phorton1/Arduino-teensyExpression/docs/ftp/hardware_patches.csv

Patch No: | Patch Name: | Patch Hold Mode: | Patch Split Low: | Patch Split High: | Patch Arp. Mode: | Patch Arp. Speed: | Patch Arp. Length: | Patch Pick Sens.: | Sound1 Program: | Sound1 Bank LSB: | Sound1 Bank MSB: | Sound1 Quantize Mode: | Sound1 Transpose: | Sound1 Volume: | Sound1 Dynamics Sens: | Sound1 Dynamics Offs: | Sound1 Reverb: | Sound2 Program: | Sound2 Bank LSB: | Sound2 Bank MSB: | Sound2 Quantize Mode: | Sound2 Transpose: | Sound2 Volume: | Sound2 Dynamics Sens: | Sound2 Dynamics Offs: | Sound2 Reverb: | Sound3 Program: | Sound3 Bank LSB: | Sound3 Bank MSB: | Sound3 Quantize Mode: | Sound3 Transpose: | Sound3 Volume: | Sound3 Dynamics Sens: | Sound3 Dynamics Offs: | Sound3 Reverb: | Sound4 Program: | Sound4 Bank LSB: | Sound4 Bank MSB: | Sound4 Quantize Mode: | Sound4 Transpose: | Sound4 Volume: | Sound4 Dynamics Sens: | Sound4 Dynamics Offs: | Sound4 Reverb: | Hold Program: | Hold Bank LSB: | Hold Bank MSB: | Hold Quantize Mode: | Hold Transpose: | Hold Volume: | Hold Dynamics Sens: | Hold Dynamics Offs: | Hold Reverb: | Mono/Poly: | Sound1 Enable: | Sound2 Enable: | Sound3 Enable: | Sound4 Enable: | Hold Enable:
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
