phorton1/Arduino-teensyExpression/docs/images/hardware-board_v7.big.jpg

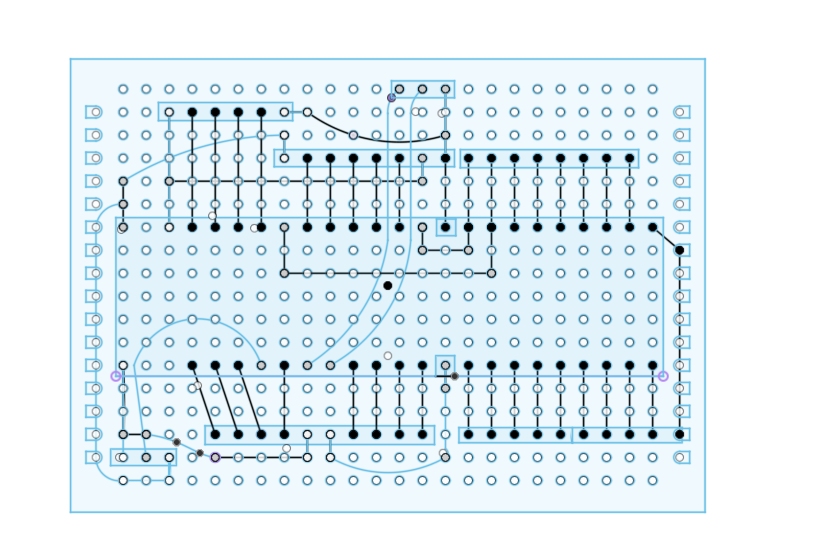
docs/images/hardware-board_v7.big.jpg
