phorton1/Arduino-teensyExpression/docs/images/hardware-micro_usb.jpg

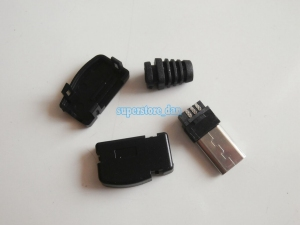
docs/images/hardware-micro_usb.jpg
