phorton1/Arduino-teensyExpression/docs/images/hardware-serial_port.big.jpg

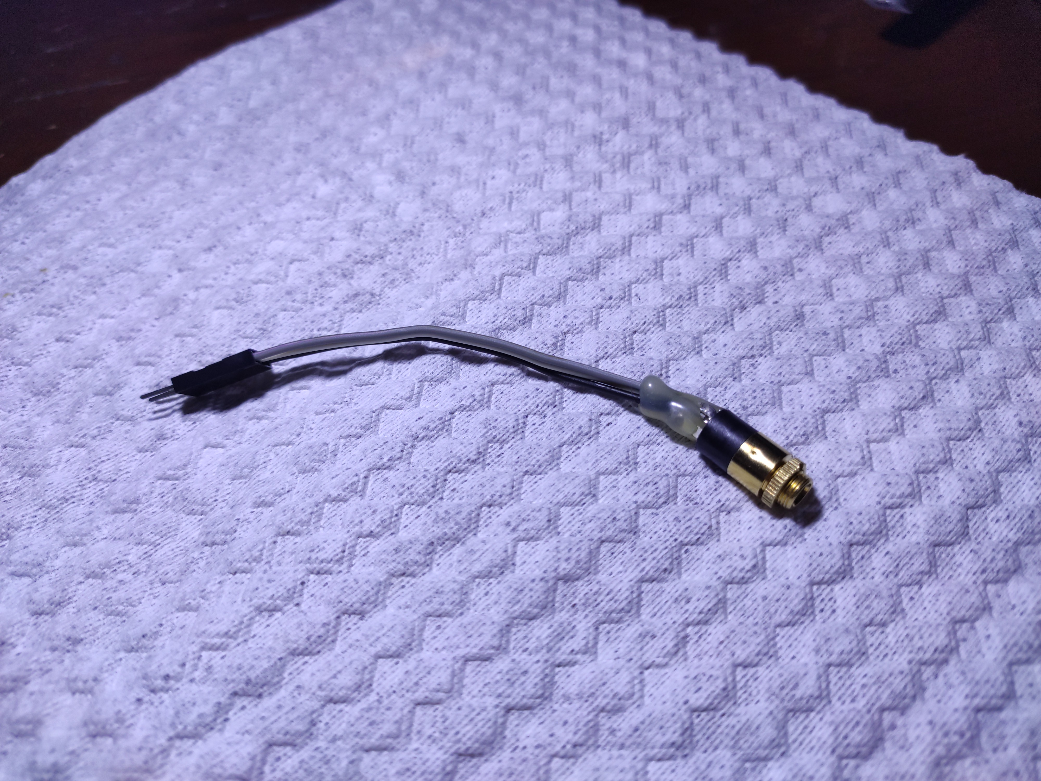
docs/images/hardware-serial_port.big.jpg
