phorton1/Arduino-teensyExpression/docs/images/teensyExpression17.jpg

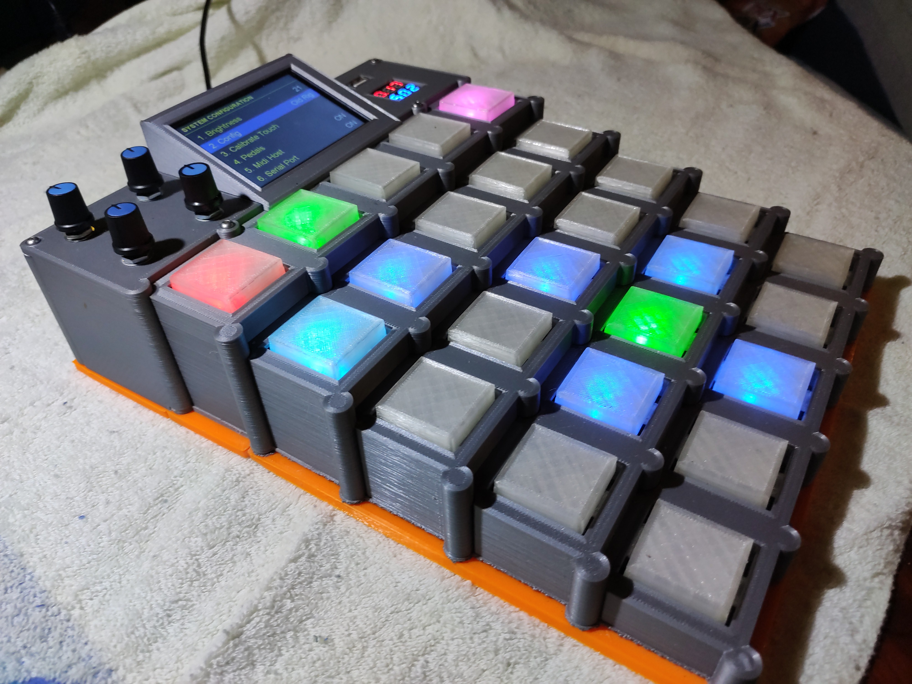
docs/images/teensyExpression17.jpg
