phorton1/Arduino-teensyExpression/docs/images/ui_configMidiMonitor.jpg

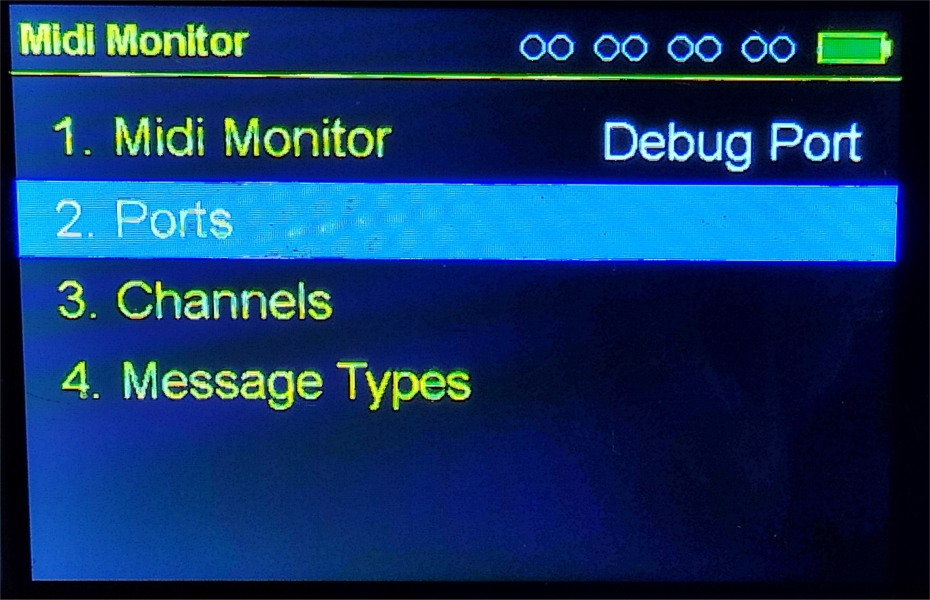
docs/images/ui_configMidiMonitor.jpg
