phorton1/Arduino-teensyExpression/docs/images/ui_configSystem_wide.jpg

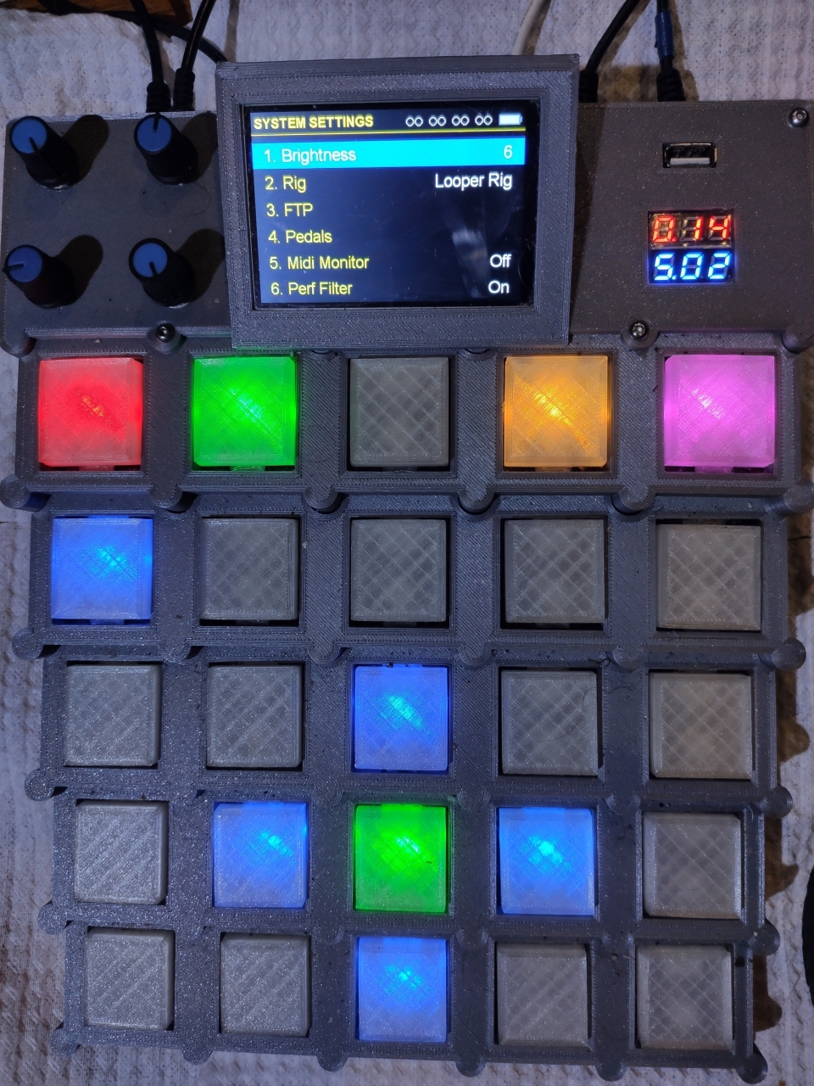
docs/images/ui_configSystem_wide.jpg
