phorton1/Arduino-teensyExpression/docs/images/ui_LooperRig_wide.jpg

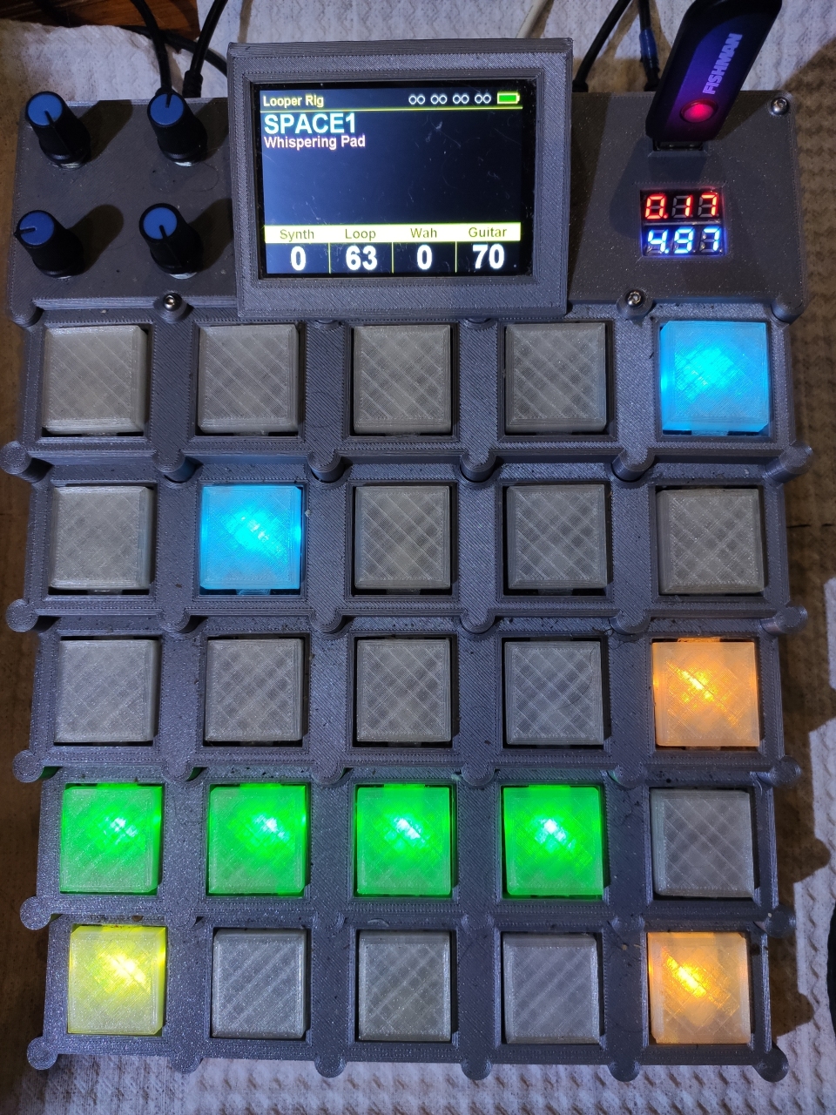
docs/images/ui_LooperRig_wide.jpg
