phorton1/Arduino-teensyExpression/docs/images/ui_LooperRig_withSong.jpg

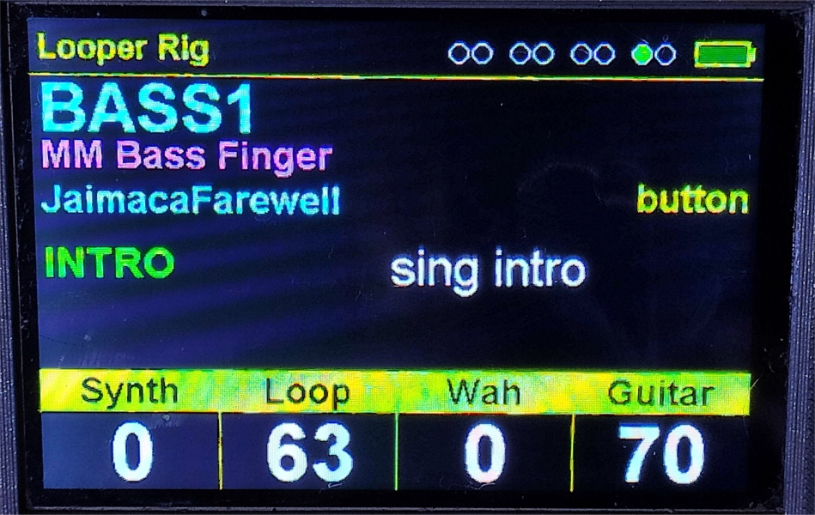
docs/images/ui_LooperRig_withSong.jpg
