phorton1/Arduino-teensyExpression/docs/images/ui_QuickMode_wide.jpg

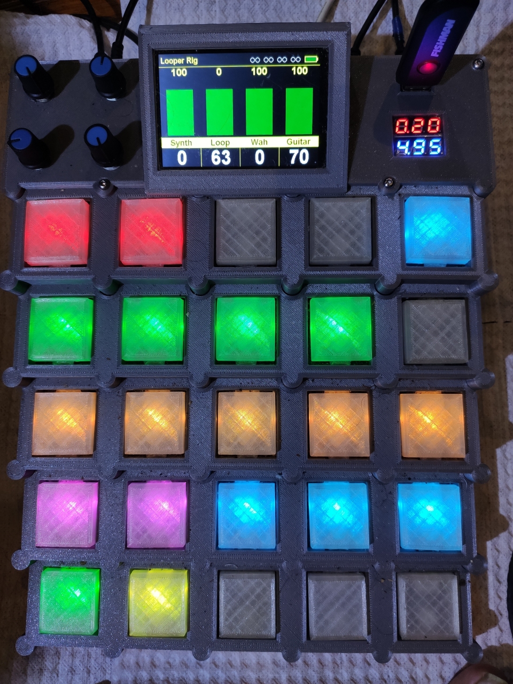
docs/images/ui_QuickMode_wide.jpg
