phorton1/Arduino-teensyExpression/docs/images/ui_selectSong.jpg

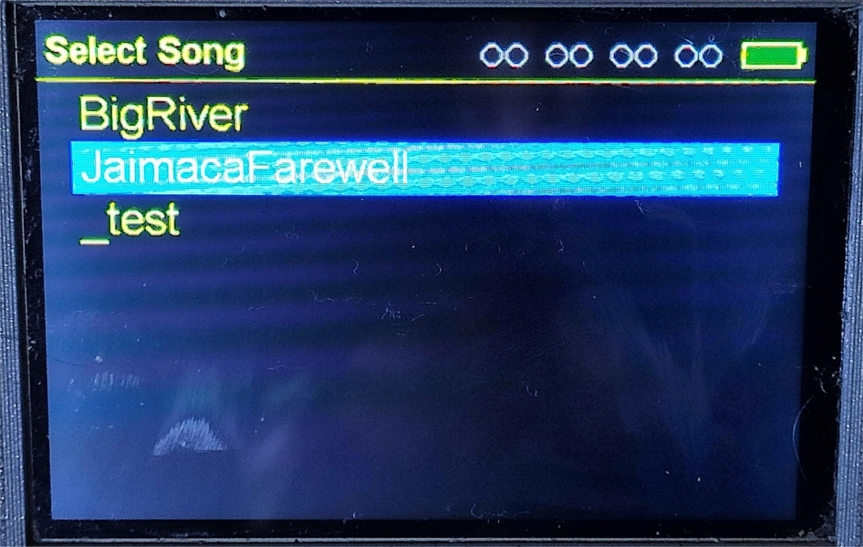
docs/images/ui_selectSong.jpg
