phorton1/Arduino-teensyExpression/docs/images/ui_songText.jpg

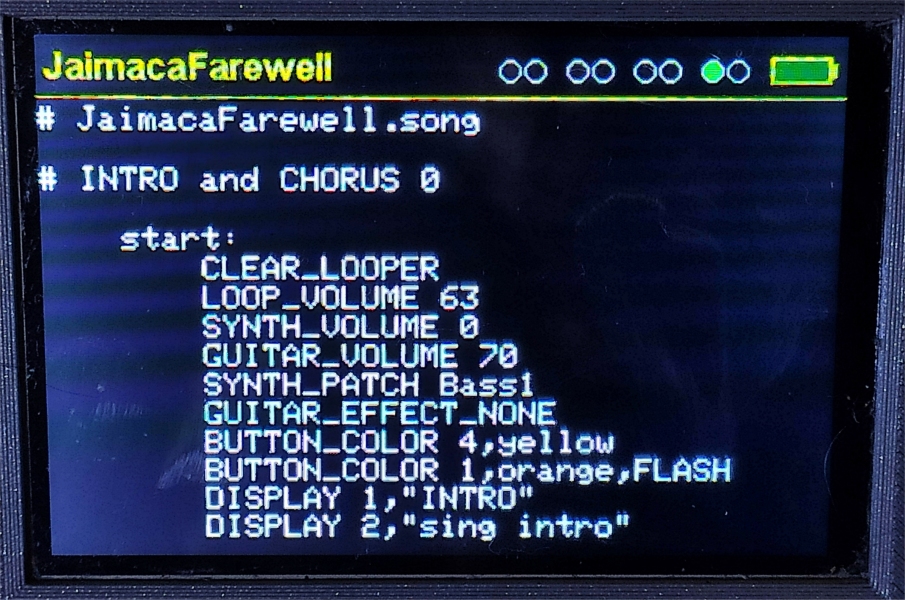
docs/images/ui_songText.jpg
