phorton1/Arduino-teensyExpression/docs/stl/display_case.stl

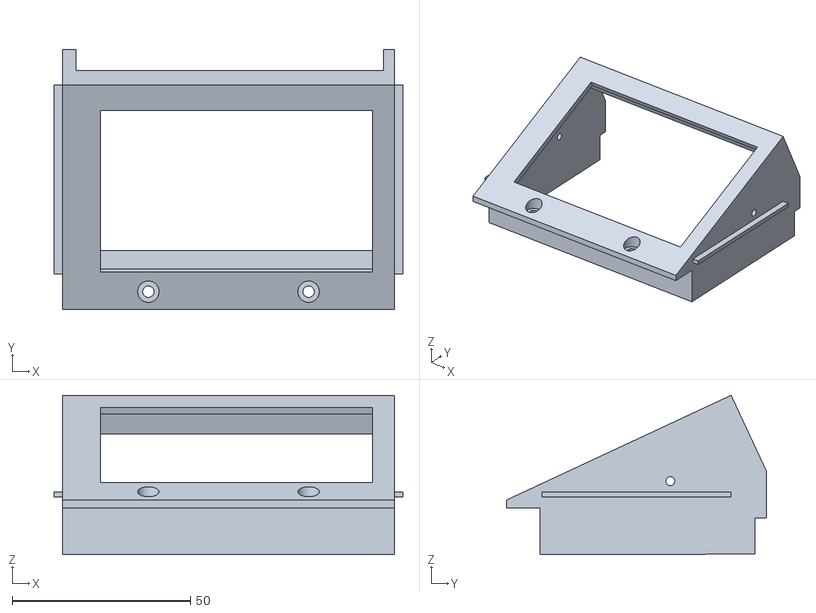
[picture p77: CAD file, 2025-01-11]
docs/stl/display_case.stl
98.0 x 73.0 x 44.8
