phorton1/Arduino-teensyExpression/docs/prusa/top5.3mf

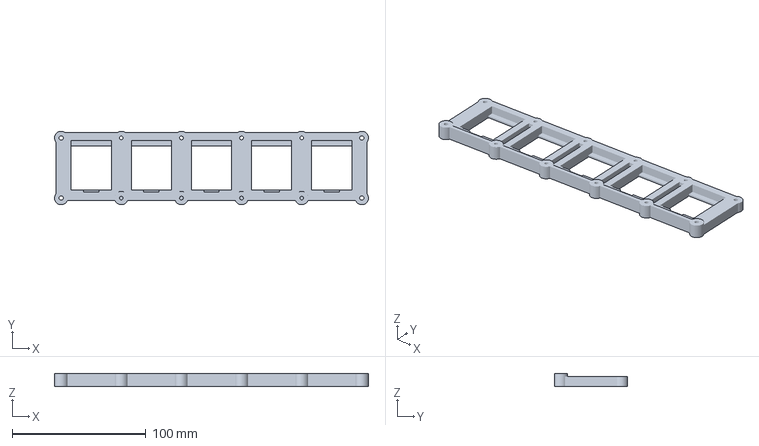
[picture p78: CAD file, 2025-01-11]
docs/prusa/top5.3mf
235.0 x 55.0 x 9.80 mm
