phorton1/Arduino-teensyExpression/docs/prusa/top_left.3mf

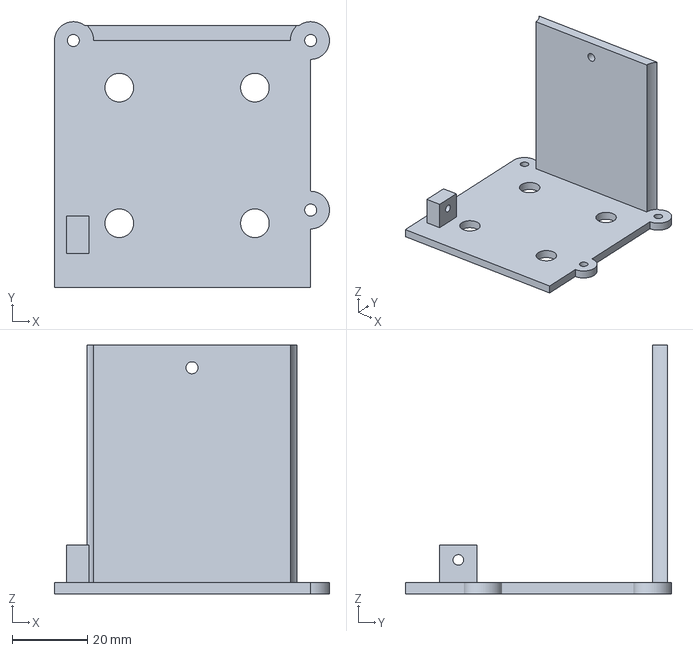
[picture p79: CAD file, 2025-01-11]
docs/prusa/top_left.3mf
73.0 x 70.5 x 66.0 mm
