phorton1/Arduino-teensyExpression/docs/stl/display_insert.stl

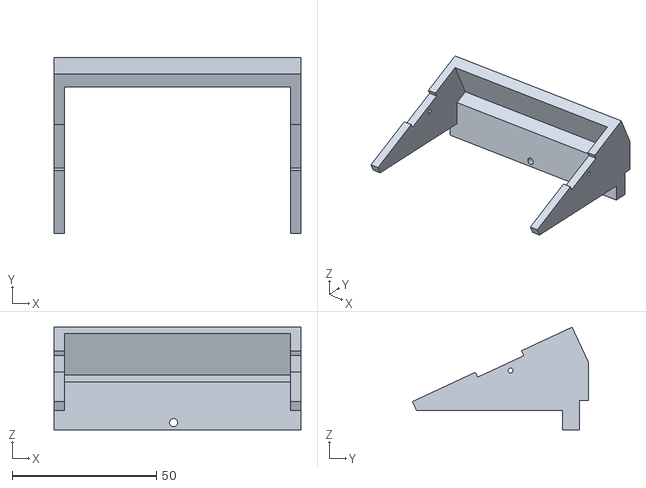
[picture p80: CAD file, 2025-01-11]
docs/stl/display_insert.stl
85.5 x 61.0 x 35.5
