phorton1/Arduino-teensyExpression/docs/prusa/display_insert.3mf

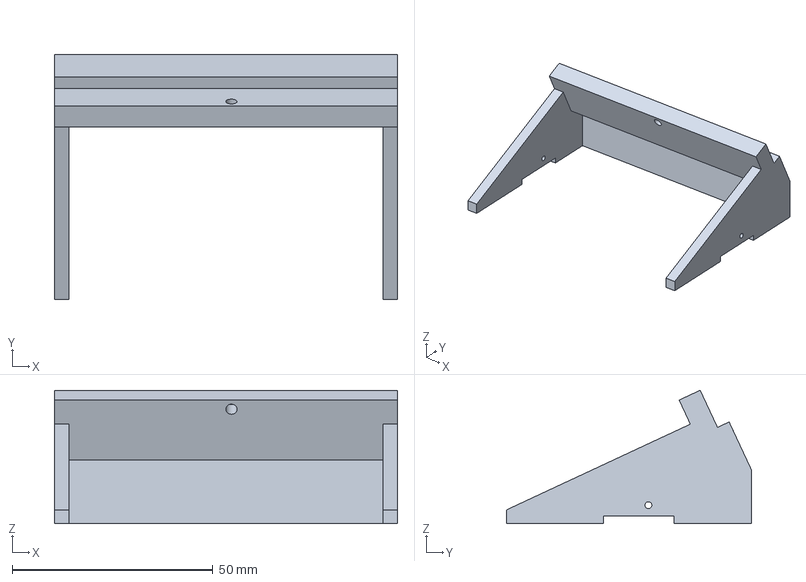
[picture p81: CAD file, 2025-01-11]
docs/prusa/display_insert.3mf
85.5 x 61.0 x 33.3 mm
