phorton1/Arduino-teensyExpression/docs/stl/frame3.stl

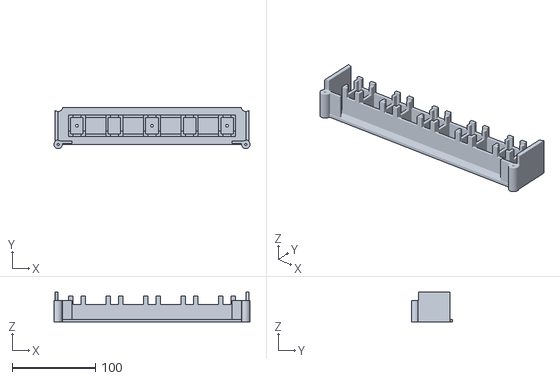
[picture p82: CAD file, 2025-01-11]
docs/stl/frame3.stl
235.0 x 49.6 x 35.5
