phorton1/Arduino-teensyExpression/docs/prusa/button_hinge_x_27.3mf

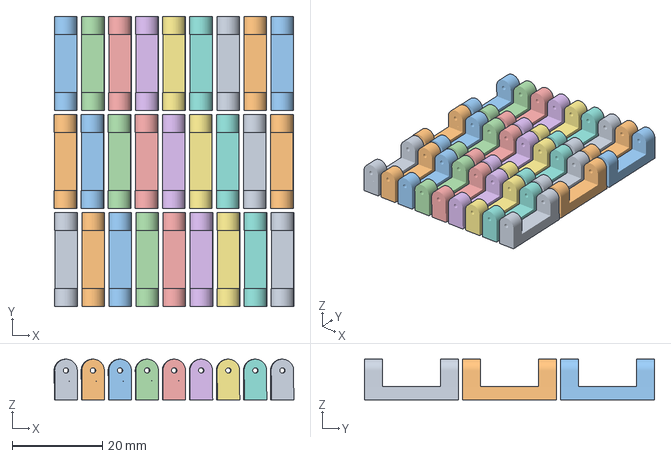
[picture p83: CAD file, 2023-08-04]
docs/prusa/button_hinge_x_27.3mf
53.2 x 64.3 x 9.00 mm
button_hinge.stl x 27
