phorton1/Arduino-teensyExpression/docs/prusa/button_base_x_5.3mf

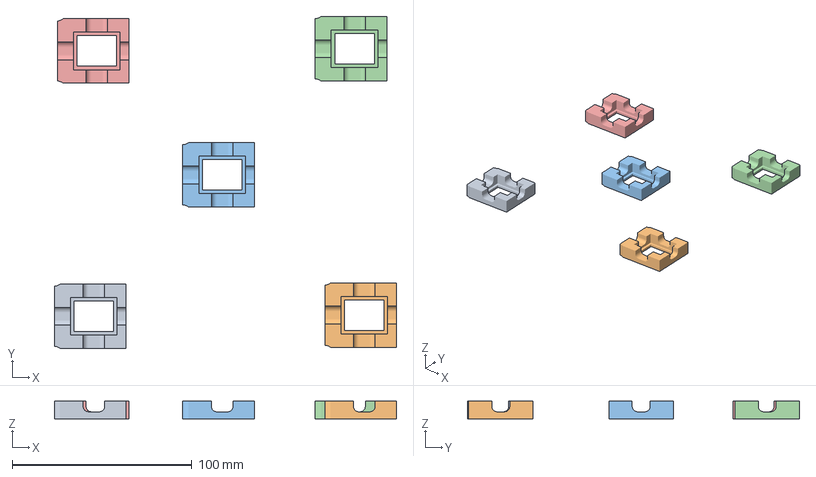
[picture p84: CAD file, 2023-08-04]
docs/prusa/button_base_x_5.3mf
190.5 x 184.8 x 10.0 mm
button_base.stl x 5
