phorton1/Arduino-teensyExpression/docs/prusa/button_top_x_5.3mf

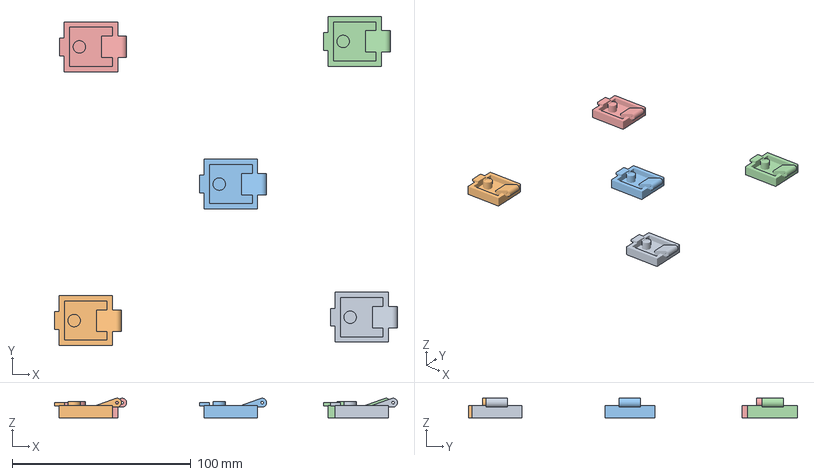
[picture p85: CAD file, 2023-08-04]
docs/prusa/button_top_x_5.3mf
192.0 x 184.3 x 11.0 mm
button_top.stl x 5
